chunter18/WASP-Final/WASP_main/headers/WASP.h

#include "wiced.h"
#include "sntp.h"
#include "WASP_i2c.h"
#include "WASP_LED.h"
#include "wasp_hibernate.h"
#include "wasp_app_dct.h"
#include "wasp_sflash_store.h"
#include "wasp_wifi_switch.h"
#include "wasp_tcp.h"
#include "wasp_udp.h"
#include "wasp_network_global.h"
#include "wasp_adxl.h"
#include "wasp_threads.h"
#include "ota2_base.h"
#include "ota2_helper.h"
#include "wiced_osl.h"
#include <inttypes.h>
