chunter18/WASP-Final/WASP_main/headers/wasp_wifi_switch.h

#define TWOG_SSID   "WASP_2.4"
#define TWOG_PASS   "BbBR977KrhAnG33Q"

#define FIVEG_SSID  "WASP_5.0"
#define FIVEG_PASS  "GSf2dSaqJYFf9Akc"


void read_write_dct(char * apSSID, char * sec_key);
wiced_result_t switch_networks(int networknum);
